Blargedy/Tefnut/6mm_OD_Tubing_to_MMU_Adapter/images/IMG_20190815_175541.jpg

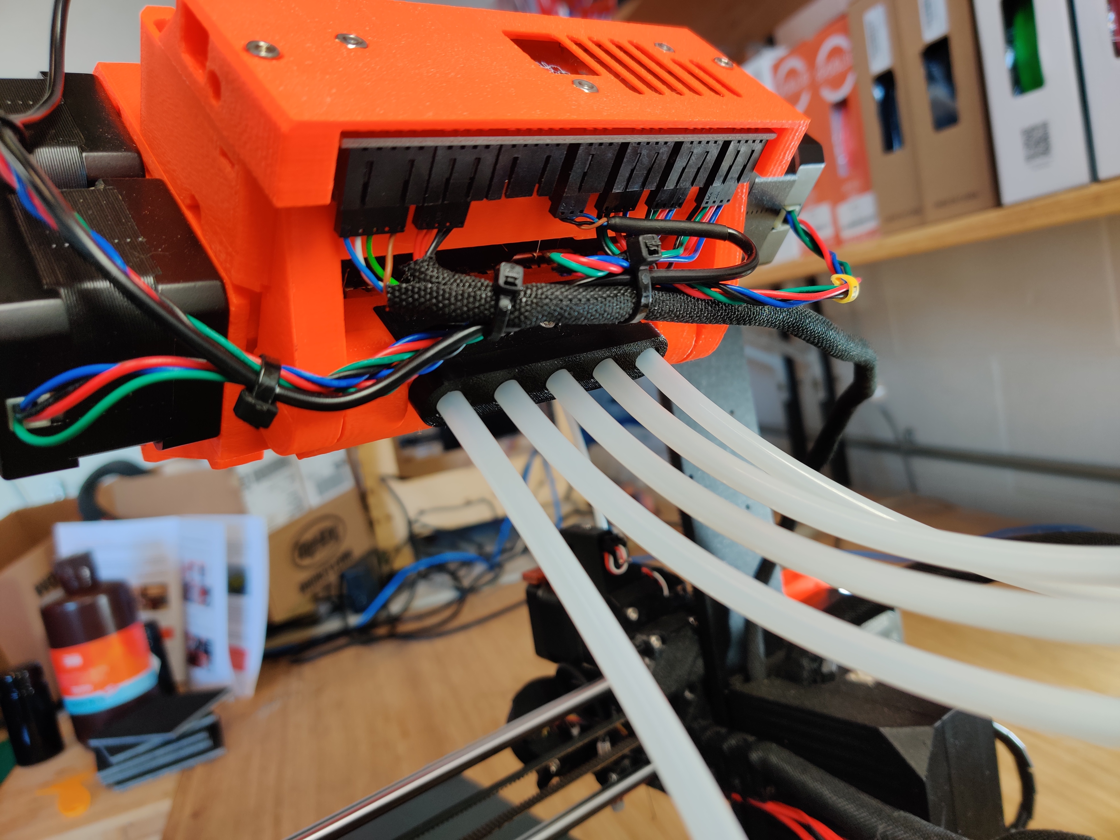
6mm_OD_Tubing_to_MMU_Adapter/images/IMG_20190815_175541.jpg
