Blargedy/Tefnut/6mm_OD_Tubing_to_MMU_Adapter/images/photo_2019-08-15_18-01-45.jpg

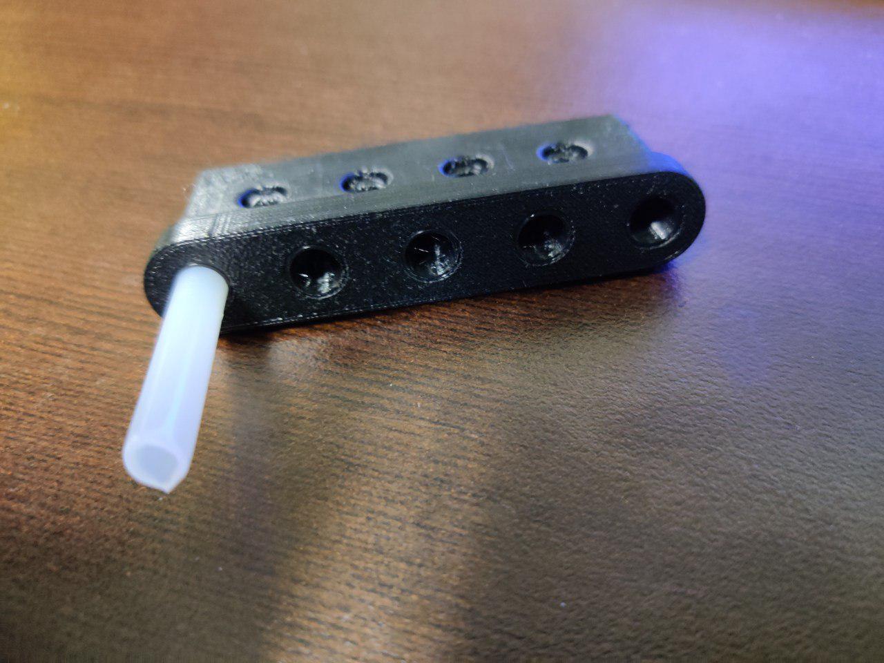
6mm_OD_Tubing_to_MMU_Adapter/images/photo_2019-08-15_18-01-45.jpg
