Blargedy/Tefnut/Drybox_Holder_for_Rubbermaid_1861476_Zylar_Container/images/IMG_20191105_182744.jpg

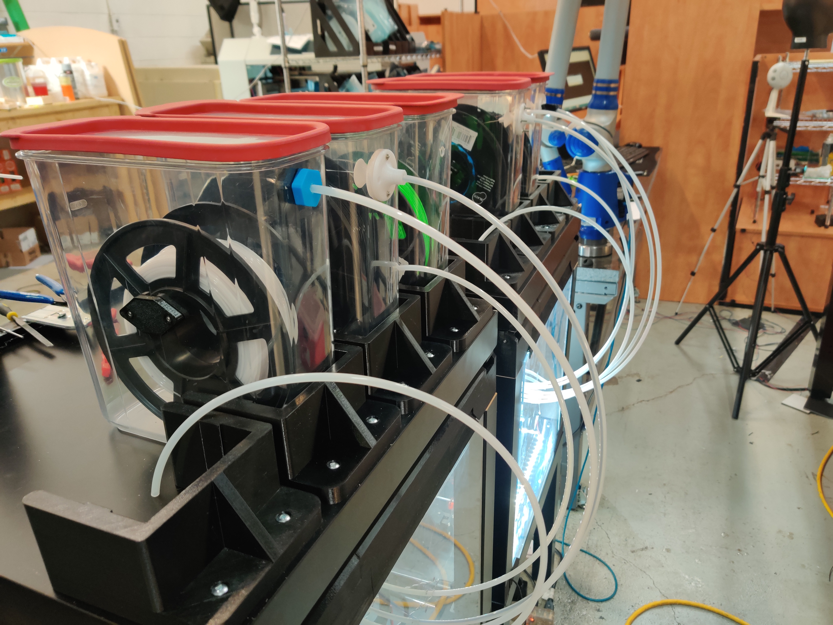
Drybox_Holder_for_Rubbermaid_1861476_Zylar_Container/images/IMG_20191105_182744.jpg
