Blargedy/Tefnut/Drybox_Holder_for_Rubbermaid_1861476_Zylar_Container/images/PartTopView.png

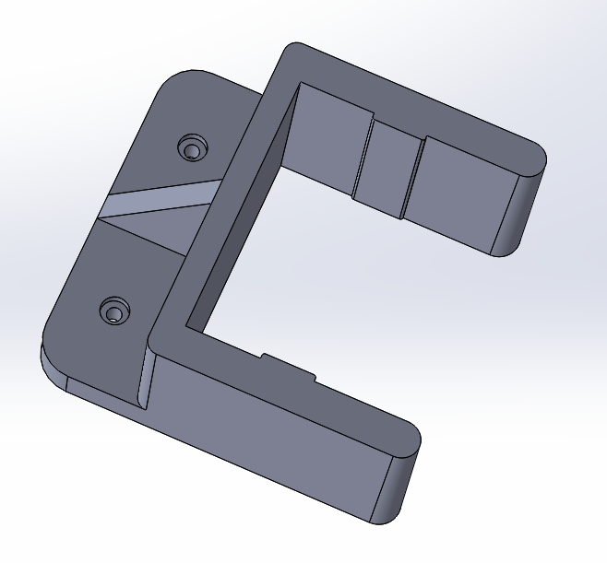
Drybox_Holder_for_Rubbermaid_1861476_Zylar_Container/images/PartTopView.png
