Blargedy/Tefnut/Enclosure_Lid_Safety-Harness/images/IMG_20191105_113403.jpg

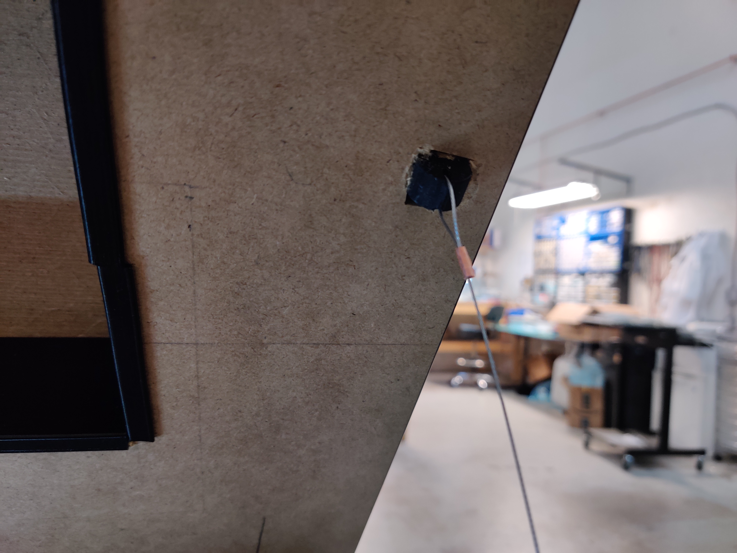
Enclosure_Lid_Safety-Harness/images/IMG_20191105_113403.jpg
