Blargedy/Tefnut/Enclosure_Lid_Safety-Harness/images/IMG_20191105_113437.jpg

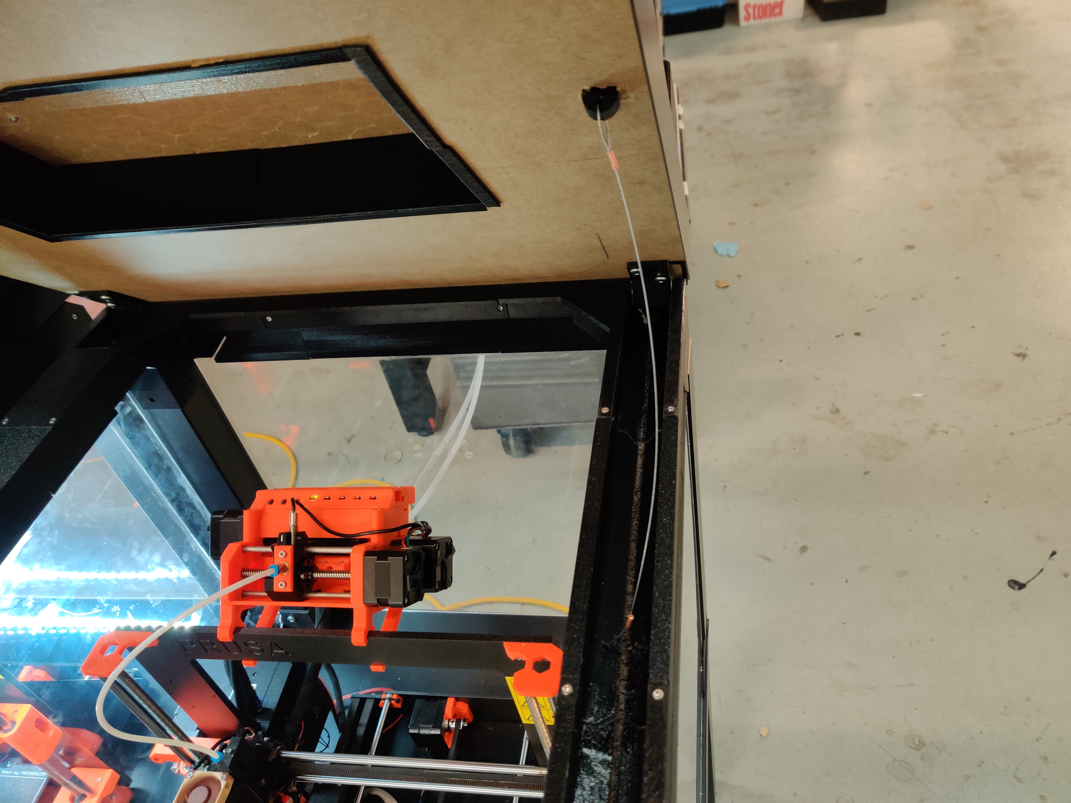
Enclosure_Lid_Safety-Harness/images/IMG_20191105_113437.jpg
