Blargedy/Tefnut/Enclosure_Lid_Safety-Harness/images/LidHarness_v1.1.png

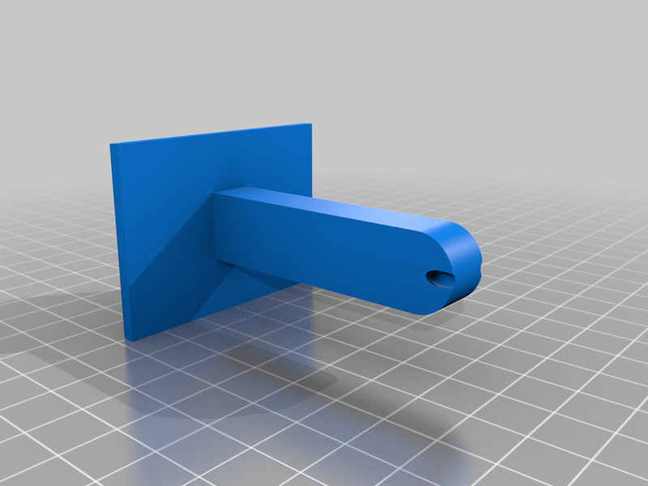
Enclosure_Lid_Safety-Harness/images/LidHarness_v1.1.png
