Blargedy/Tefnut/Individual-Spool_Dry-box_Inserts_and_Modified_Universal_Auto-Rewind_Spool_Holder/images/AxleAndHolderShowingSlottedEnd.png

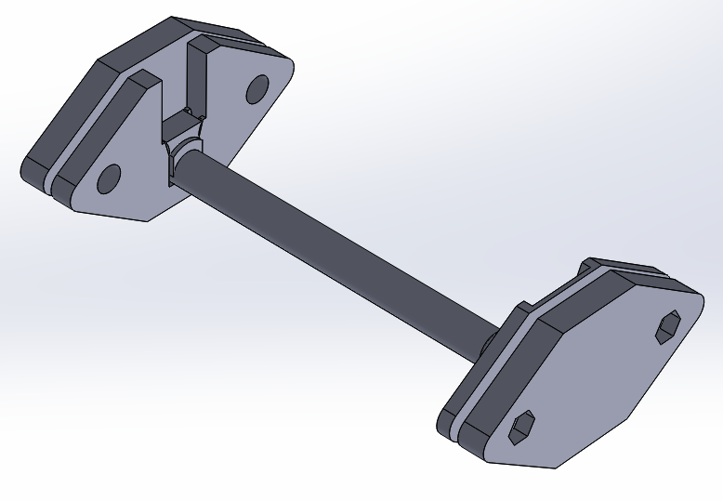
Individual-Spool_Dry-box_Inserts_and_Modified_Universal_Auto-Rewind_Spool_Holder/images/AxleAndHolderShowingSlottedEnd.png
