Blargedy/Tefnut/Individual-Spool_Dry-box_Inserts_and_Modified_Universal_Auto-Rewind_Spool_Holder/images/IMG_20190927_110512.jpg

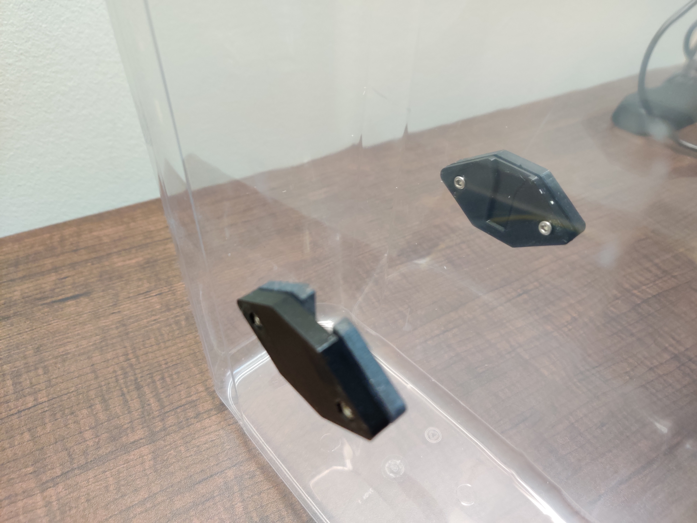
Individual-Spool_Dry-box_Inserts_and_Modified_Universal_Auto-Rewind_Spool_Holder/images/IMG_20190927_110512.jpg
