Blargedy/Tefnut/Individual-Spool_Dry-box_Inserts_and_Modified_Universal_Auto-Rewind_Spool_Holder/images/IMG_20191031_165605.jpg

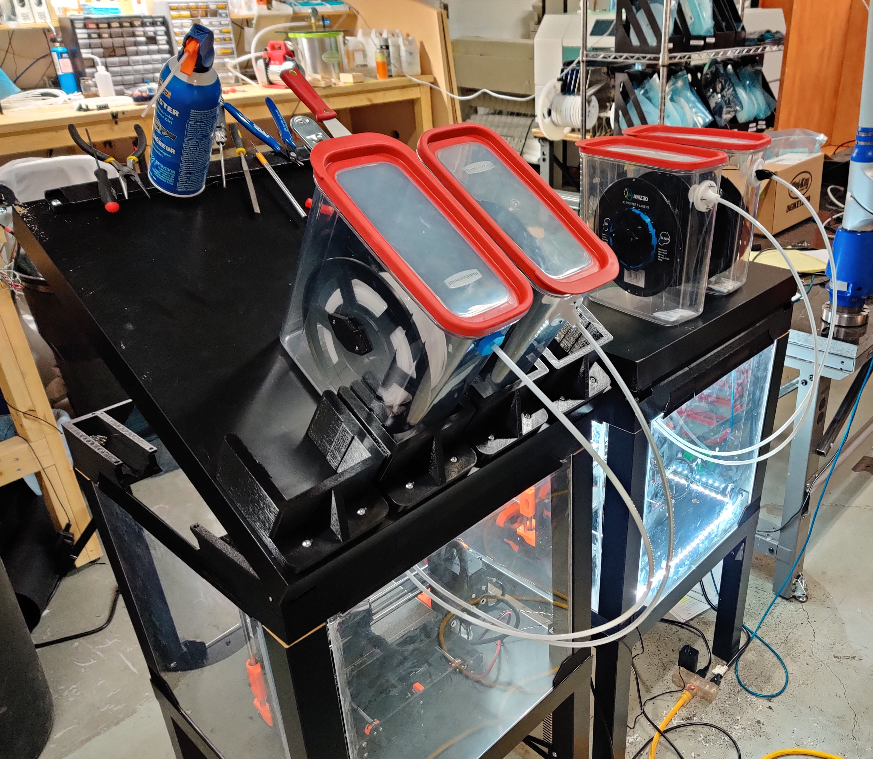
Individual-Spool_Dry-box_Inserts_and_Modified_Universal_Auto-Rewind_Spool_Holder/images/IMG_20191031_165605.jpg
