Blargedy/Tefnut/Push-Fit_Tube_Holders_For_6mm_Outer_Diameter_Tubing/images/2021-07-27_21_03_31-Autodesk_Fusion_360.png

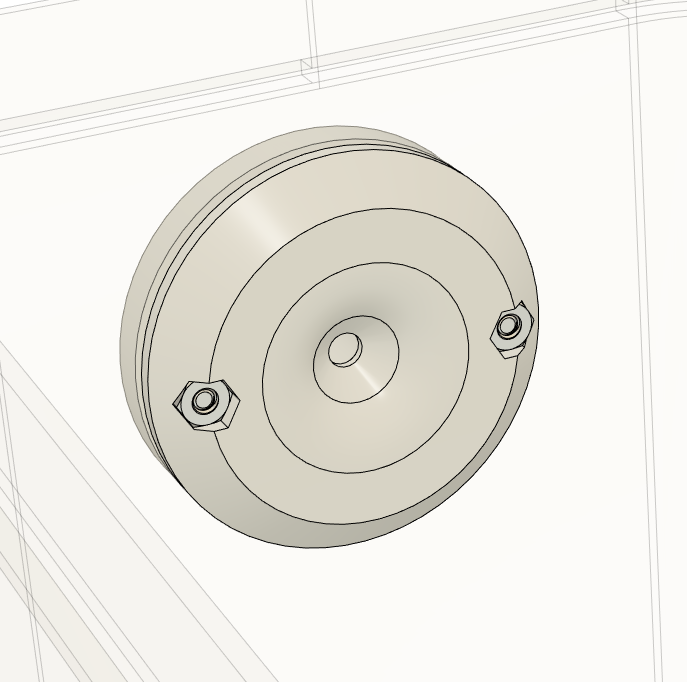
Push-Fit_Tube_Holders_For_6mm_Outer_Diameter_Tubing/images/2021-07-27_21_03_31-Autodesk_Fusion_360.png
