Blargedy/Tefnut/Push-Fit_Tube_Holders_For_6mm_Outer_Diameter_Tubing/images/InsideFitment.png

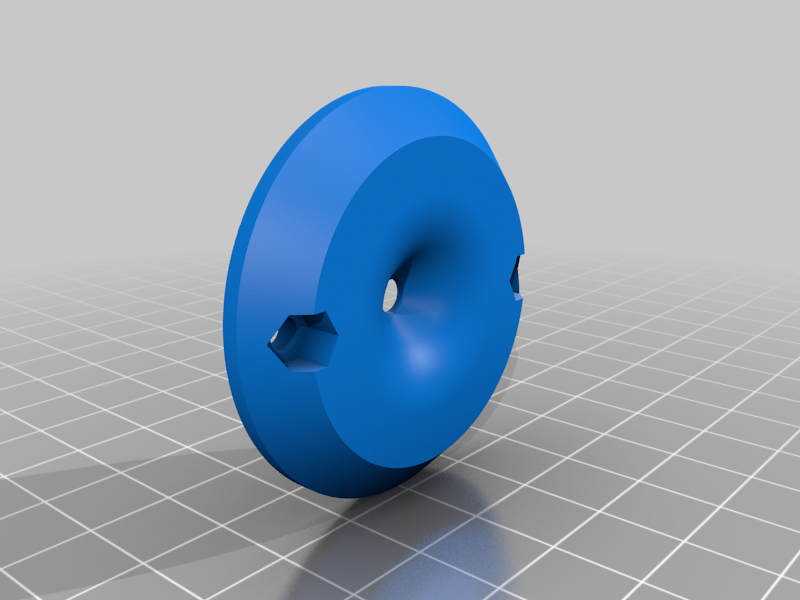
Push-Fit_Tube_Holders_For_6mm_Outer_Diameter_Tubing/images/InsideFitment.png
