Blargedy/Tefnut/Push-Fit_Tube_Holders_For_6mm_Outer_Diameter_Tubing/images/OutsideFitment.png

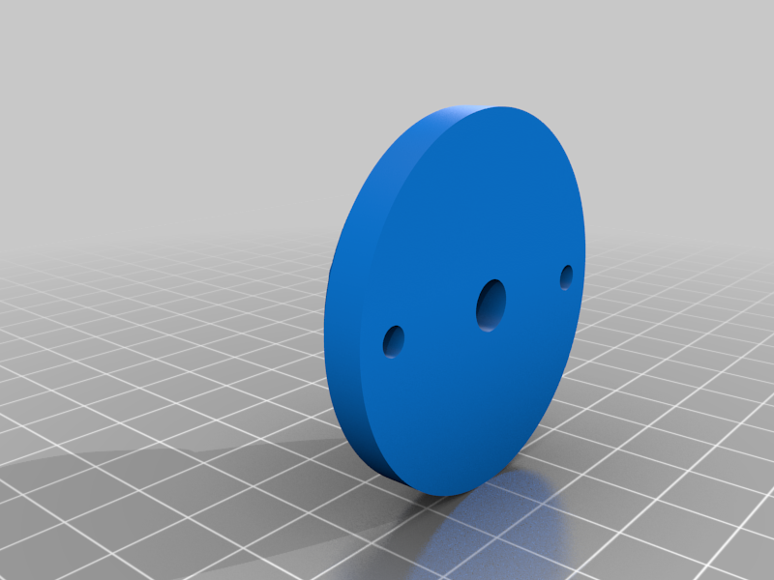
Push-Fit_Tube_Holders_For_6mm_Outer_Diameter_Tubing/images/OutsideFitment.png
