Blargedy/Tefnut/Push-Fit_Tube_Holders_For_6mm_Outer_Diameter_Tubing/images/photo_2021-07-27_21-06-22.jpg

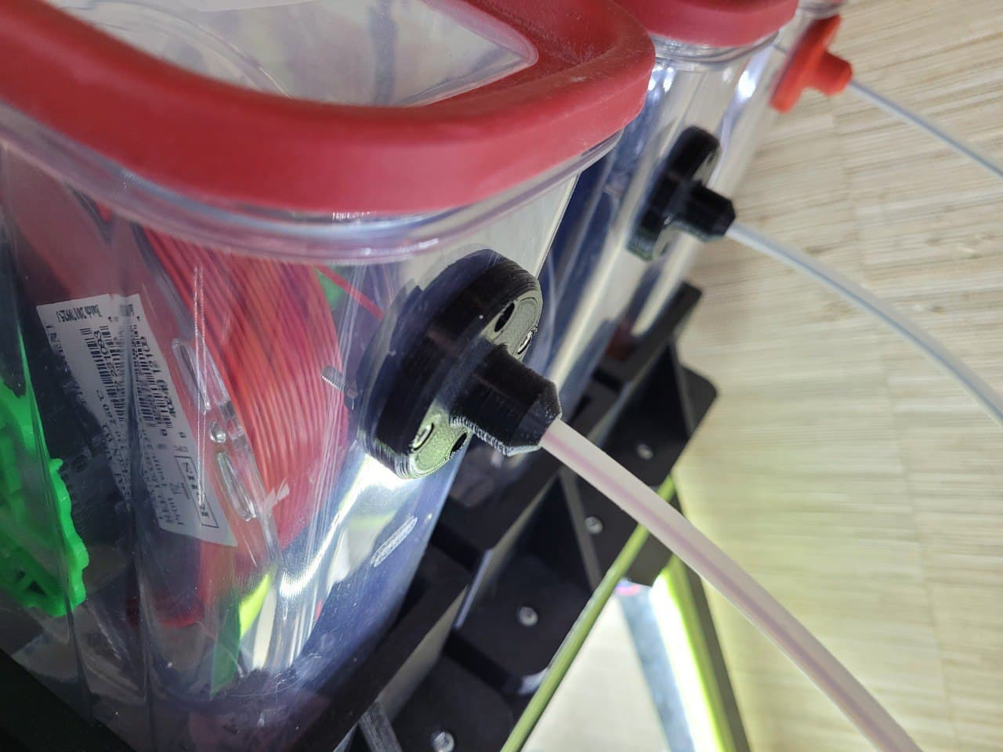
Push-Fit_Tube_Holders_For_6mm_Outer_Diameter_Tubing/images/photo_2021-07-27_21-06-22.jpg
